fl0m0/ReBox/doc/datasheets/switch/1533612989.png

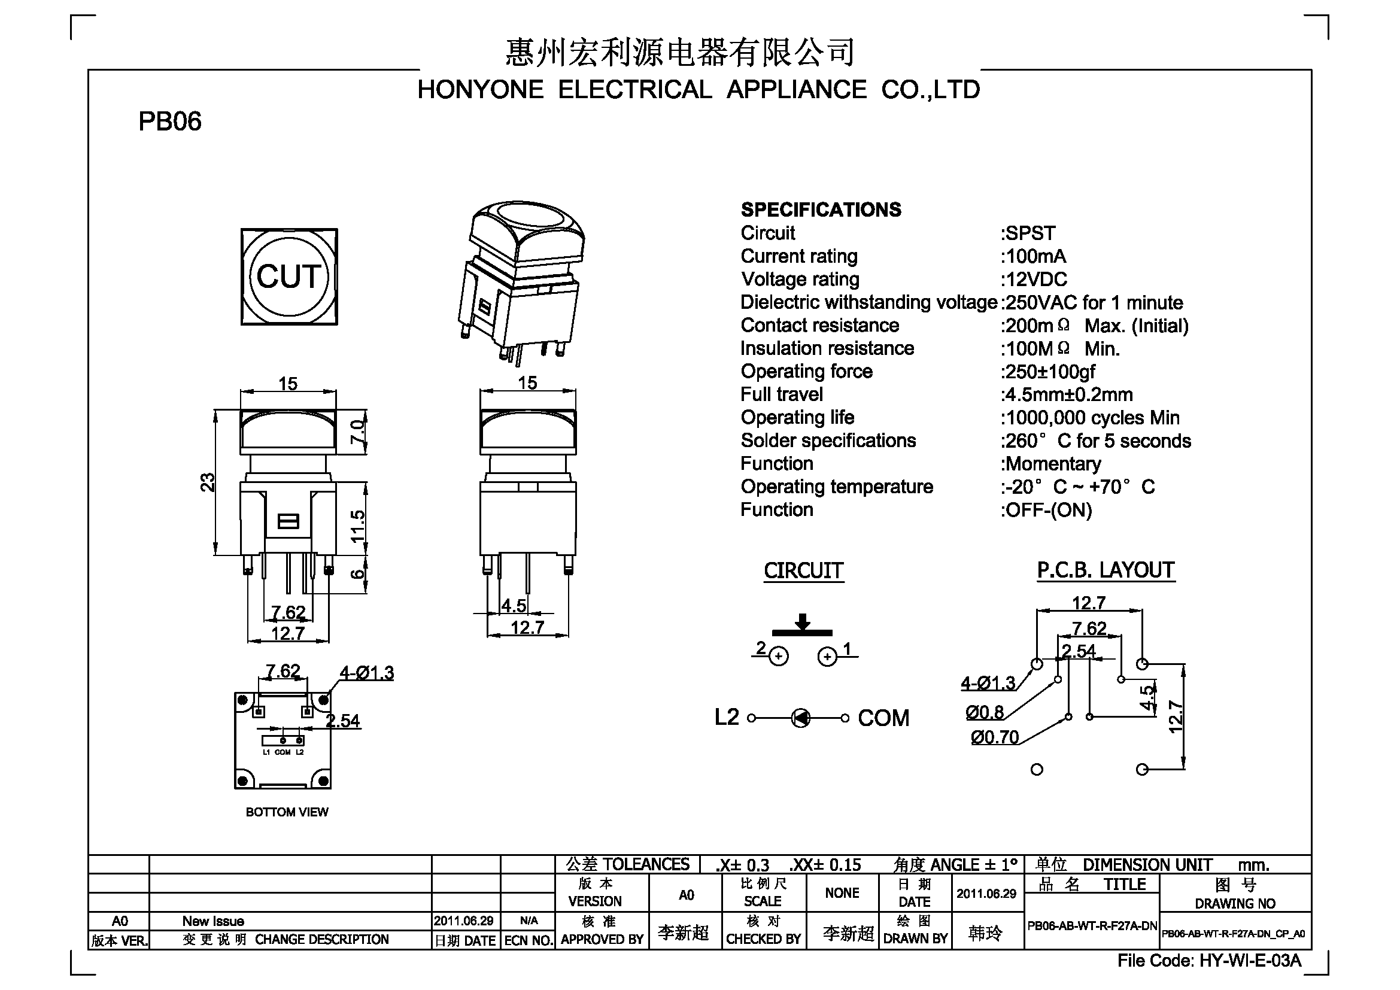
doc/datasheets/switch/1533612989.png
