fl0m0/ReBox/doc/datasheets/switch/20211209145039_88595.jpg

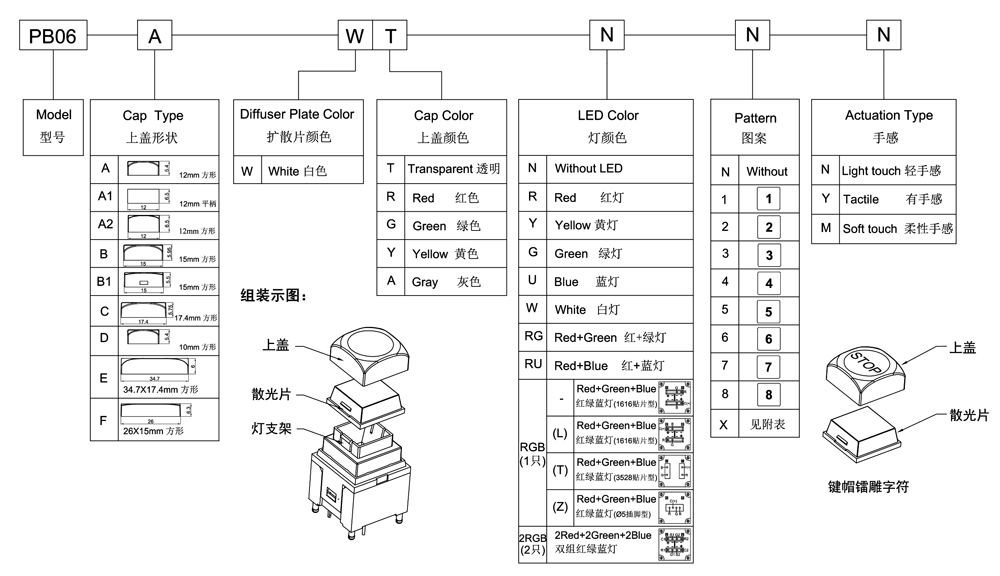
doc/datasheets/switch/20211209145039_88595.jpg
