fl0m0/ReBox/doc/datasheets/switch/20211209151750_96506.jpg

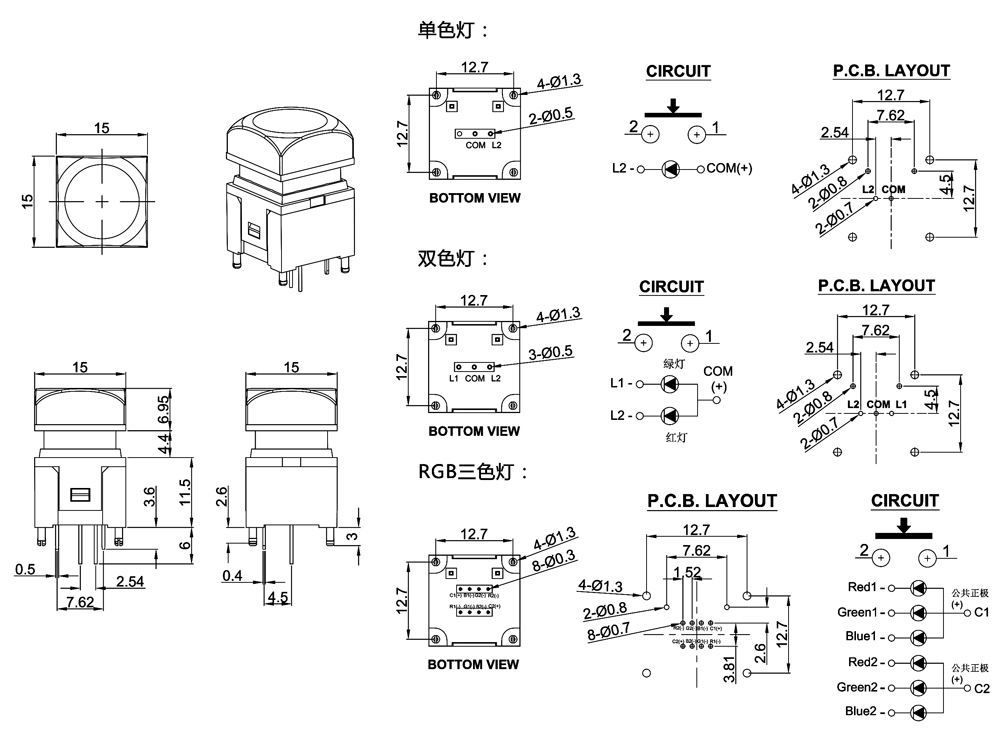
doc/datasheets/switch/20211209151750_96506.jpg
