fl0m0/ReBox/sim/relay_driver.asc

C1: cap; 22µ; Rser=0.2
C2: cap; 470n
D1: schottky; BAT54
D2: zener; BZX84B12VL
L1: ind; 200m
M1: nmos; BSH103BK
M2: nmos; BSH103BK
R1: res; 46
R2: res; 330k
R3: res; 47
V1: voltage; 5; Rser=0.1
V2: voltage; PULSE(0 5 1m 10n 10n 250m 300m)
Named nets: 0, +5, Drain, Gate1, Gate2
.tran 310m
.inc BSH103BK.lib
