fl0m0/ReBox/pcb/ReBox_A1/MCU.kicad_sch

## KiCad design pcb/ReBox_A1/MCU.kicad_sch (2025-03-04)

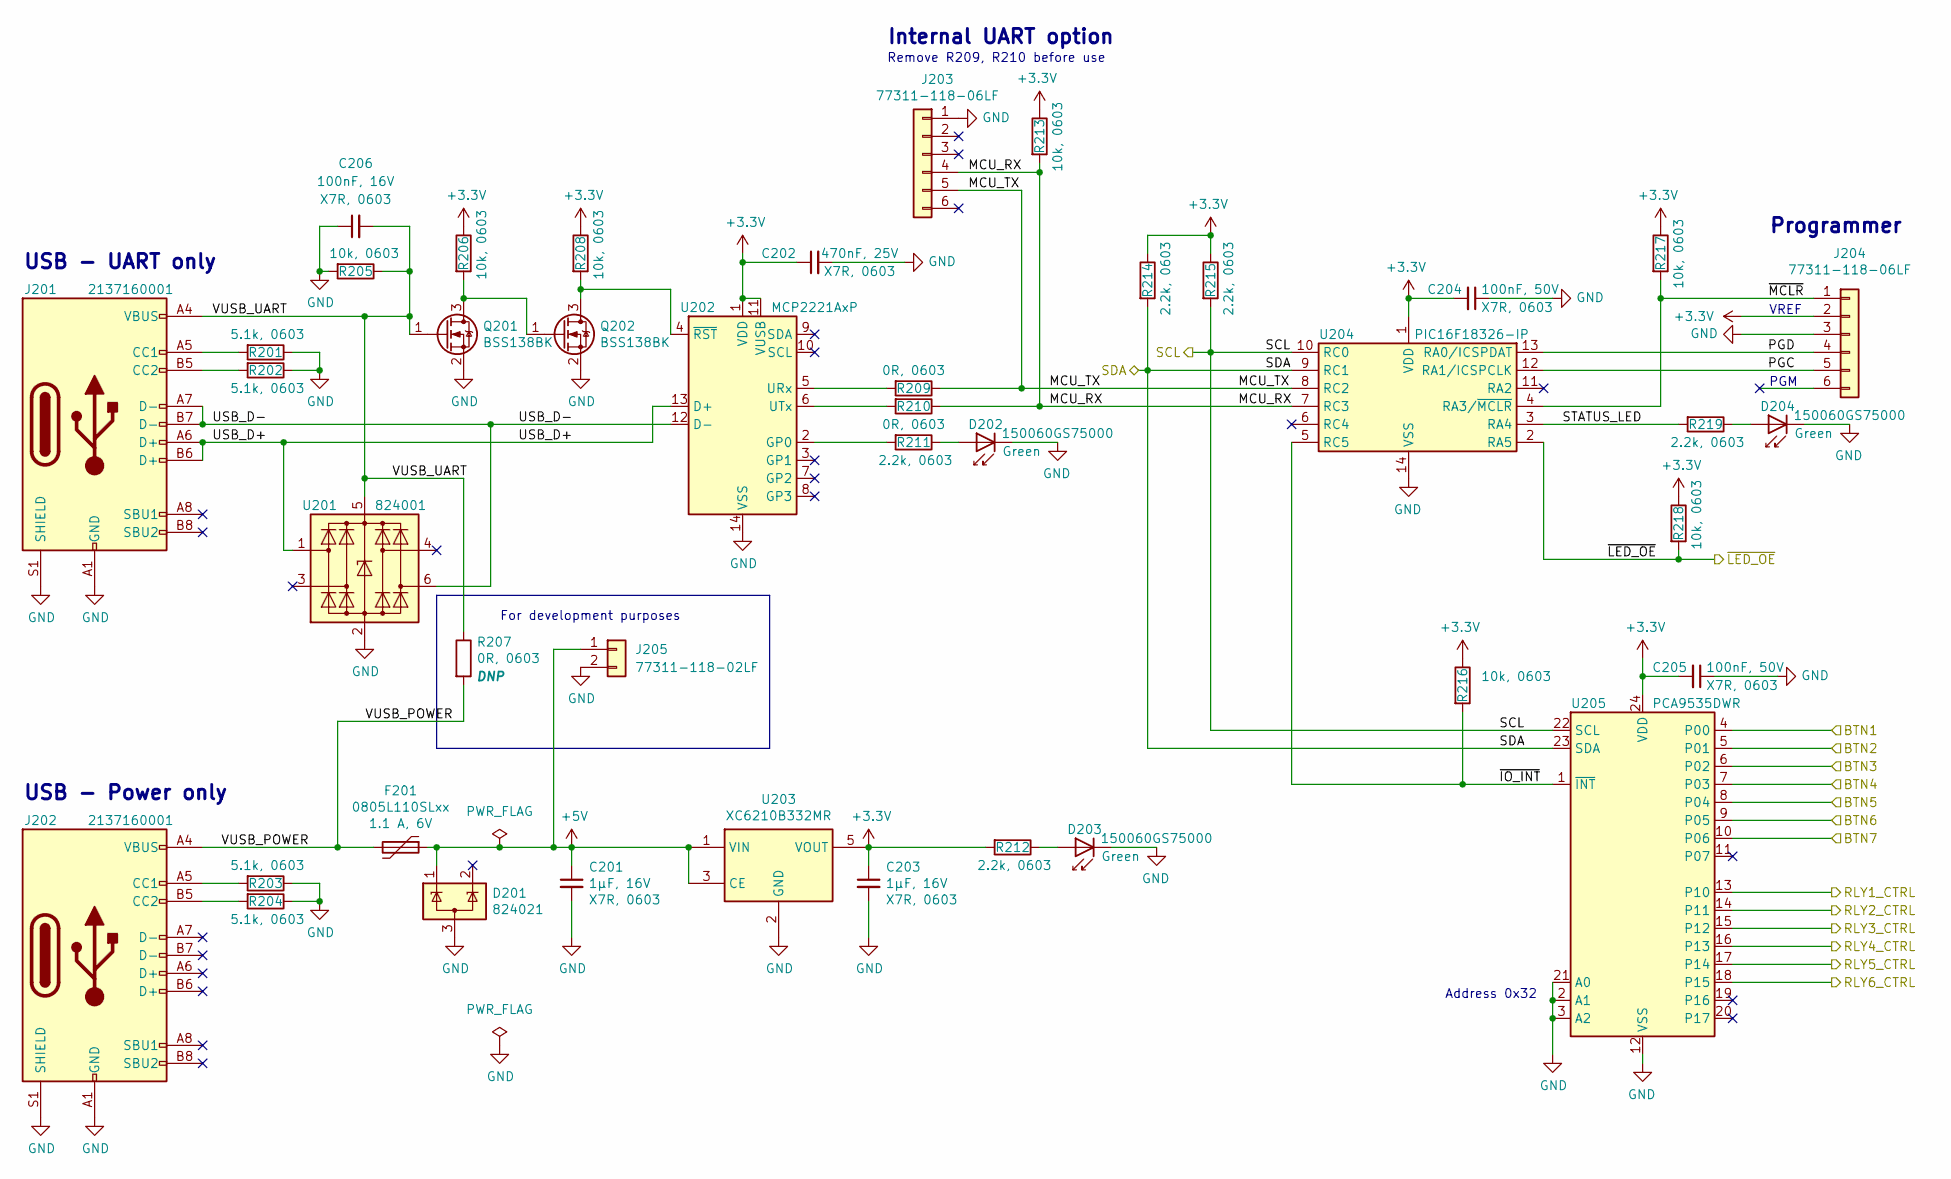
[picture p20: schematic MCU.kicad_sch]

Parts:
C201, C203: 1uF,16V,X7R,0603; C_0603_1608Metric_Pad1.08x0.95mm_HandSolder
C202: 470nF,25V,X7R,0603; C_0603_1608Metric_Pad1.08x0.95mm_HandSolder
C204, C205: 100nF,50V,X7R,0603; C_0603_1608Metric_Pad1.08x0.95mm_HandSolder
C206: 100nF,16V,X7R,0603; C_0603_1608Metric_Pad1.08x0.95mm_HandSolder
D201: 824021; SOT-23_Handsoldering
D202, D203, D204: 150060GS75000; LED_0603_1608Metric_Pad1.05x0.95mm_HandSolder
F201: 0805L110SLxx; Fuse_0805_2012Metric_Pad1.15x1.40mm_HandSolder
J201, J202: 2137160001; USB_C_Receptacle_Molex_2137160001
J203, J204: 77311-118-06LF; PinHeader_1x06_P2.54mm_Vertical
J205: 77311-118-02LF; PinHeader_1x02_P2.54mm_Vertical
Q201, Q202: BSS138BK; SOT-23_Handsoldering
R201, R202, R203, R204: 5.1k,0603; R_0603_1608Metric_Pad0.98x0.95mm_HandSolder
R205, R206, R208, R213, R216, R217, R218: 10k,0603; R_0603_1608Metric_Pad0.98x0.95mm_HandSolder
R207, R209, R210: 0R,0603; R_0603_1608Metric_Pad0.98x0.95mm_HandSolder
R211, R212, R214, R215, R219: 2.2k,0603; R_0603_1608Metric_Pad0.98x0.95mm_HandSolder
U201: 824001; SOT-23-6_Handsoldering
U202: MCP2221AxP; DIP-14_W7.62mm
U203: XC6210B332MR; SOT-23-5
U204: PIC16F18326-IP; DIP-14_W7.62mm
U205: PCA9535DWR; SOIC-24W_7.5x15.4mm_P1.27mm

Connections:
+3.3V: C202.1, C203.1, C204.2, C205.2, J204.2, R206.1, R208.1, R212.2, R213.1, R214.1, R215.1, R216.1, R217.1, R218.1, U202.1 (VDD), U202.11 (VUSB), U203.5 (VOUT), U204.1 (VDD), U205.24 (VDD)
+5V: C201.1, D201.1 (K), F201.1, J205.1, U203.1 (VIN), U203.3 (CE)
BTN1: U205.4 (P00)
BTN2: U205.5 (P01)
BTN3: U205.6 (P02)
BTN4: U205.7 (P03)
BTN5: U205.8 (P04)
BTN6: U205.9 (P05)
BTN7: U205.10 (P06)
GND: C201.2, C202.2, C203.2, C204.1, C205.1, C206.1, D201.3 (A), D202.1 (K), D203.1 (K), D204.1 (K), J201.A1 (GND), J201.A12 (GND), J201.B1 (GND), J201.B12 (GND), J201.S1 (SHIELD), J202.A1 (GND), J202.A12 (GND), J202.B1 (GND), J202.B12 (GND), J202.S1 (SHIELD), J203.1, J204.3, J205.2, Q201.2 (S), Q202.2 (S), R201.1, R202.1, R203.1, R204.1, R205.2, U201.2 (GND), U202.14 (VSS), U203.2 (GND), U204.14 (VSS), U205.2 (A1), U205.3 (A2), U205.12 (VSS), U205.21 (A0)
MCU_RX: J203.4, R210.1, R213.2, U204.7 (RC3)
MCU_TX: J203.5, R209.1, U204.8 (RC2)
unnamed: D202.2 (A), R211.1
unnamed: D203.2 (A), R212.1
unnamed: D204.2 (A), R219.1
unnamed: J201.A5 (CC1), R201.2
unnamed: J201.B5 (CC2), R202.2
unnamed: J202.A5 (CC1), R203.2
unnamed: J202.B5 (CC2), R204.2
unnamed: Q201.3 (D), Q202.1 (G), R206.2
unnamed: Q202.3 (D), R208.2, U202.4 (~RST)
unnamed: R209.2, U202.5 (URx)
unnamed: R210.2, U202.6 (UTx)
unnamed: R211.2, U202.2 (GP0)
PGC: J204.5, U204.12 (RA1/ICSPCLK)
PGD: J204.4, U204.13 (RA0/ICSPDAT)
RLY1_CTRL: U205.13 (P10)
RLY2_CTRL: U205.14 (P11)
RLY3_CTRL: U205.15 (P12)
RLY4_CTRL: U205.16 (P13)
RLY5_CTRL: U205.17 (P14)
RLY6_CTRL: U205.18 (P15)
SCL: R215.2, U204.10 (RC0), U205.22 (SCL)
SDA: R214.2, U204.9 (RC1), U205.23 (SDA)
STATUS_LED: R219.2, U204.3 (RA4)
USB_D+: J201.A6 (D+), J201.B6 (D+), U201.1 (I/O1), U202.13 (D+)
USB_D-: J201.A7 (D-), J201.B7 (D-), U201.6 (I/O4), U202.12 (D-)
VUSB_POWER: F201.2, J202.A4 (VBUS), J202.A9 (VBUS), J202.B4 (VBUS), J202.B9 (VBUS), R207.2
VUSB_UART: C206.2, J201.A4 (VBUS), J201.A9 (VBUS), J201.B4 (VBUS), J201.B9 (VBUS), Q201.1 (G), R205.1, R207.1, U201.5 (VBUS)
~IO_INT: R216.2, U204.5 (RC5), U205.1 (~INT)
~LED_OE: R218.2, U204.2 (RA5)
~MCLR: J204.1, R217.2, U204.4 (RA3/~MCLR)

Notes on the sheet:
Programmer
PGM
Address 0x32
Internal UART option
For development purposes
USB - UART only
Remove R209, R210 before use
VREF
USB - Power only
