fl0m0/ReBox/pcb/ReBox_A1/Relais.kicad_sch

## KiCad design pcb/ReBox_A1/Relais.kicad_sch (2025-03-04)

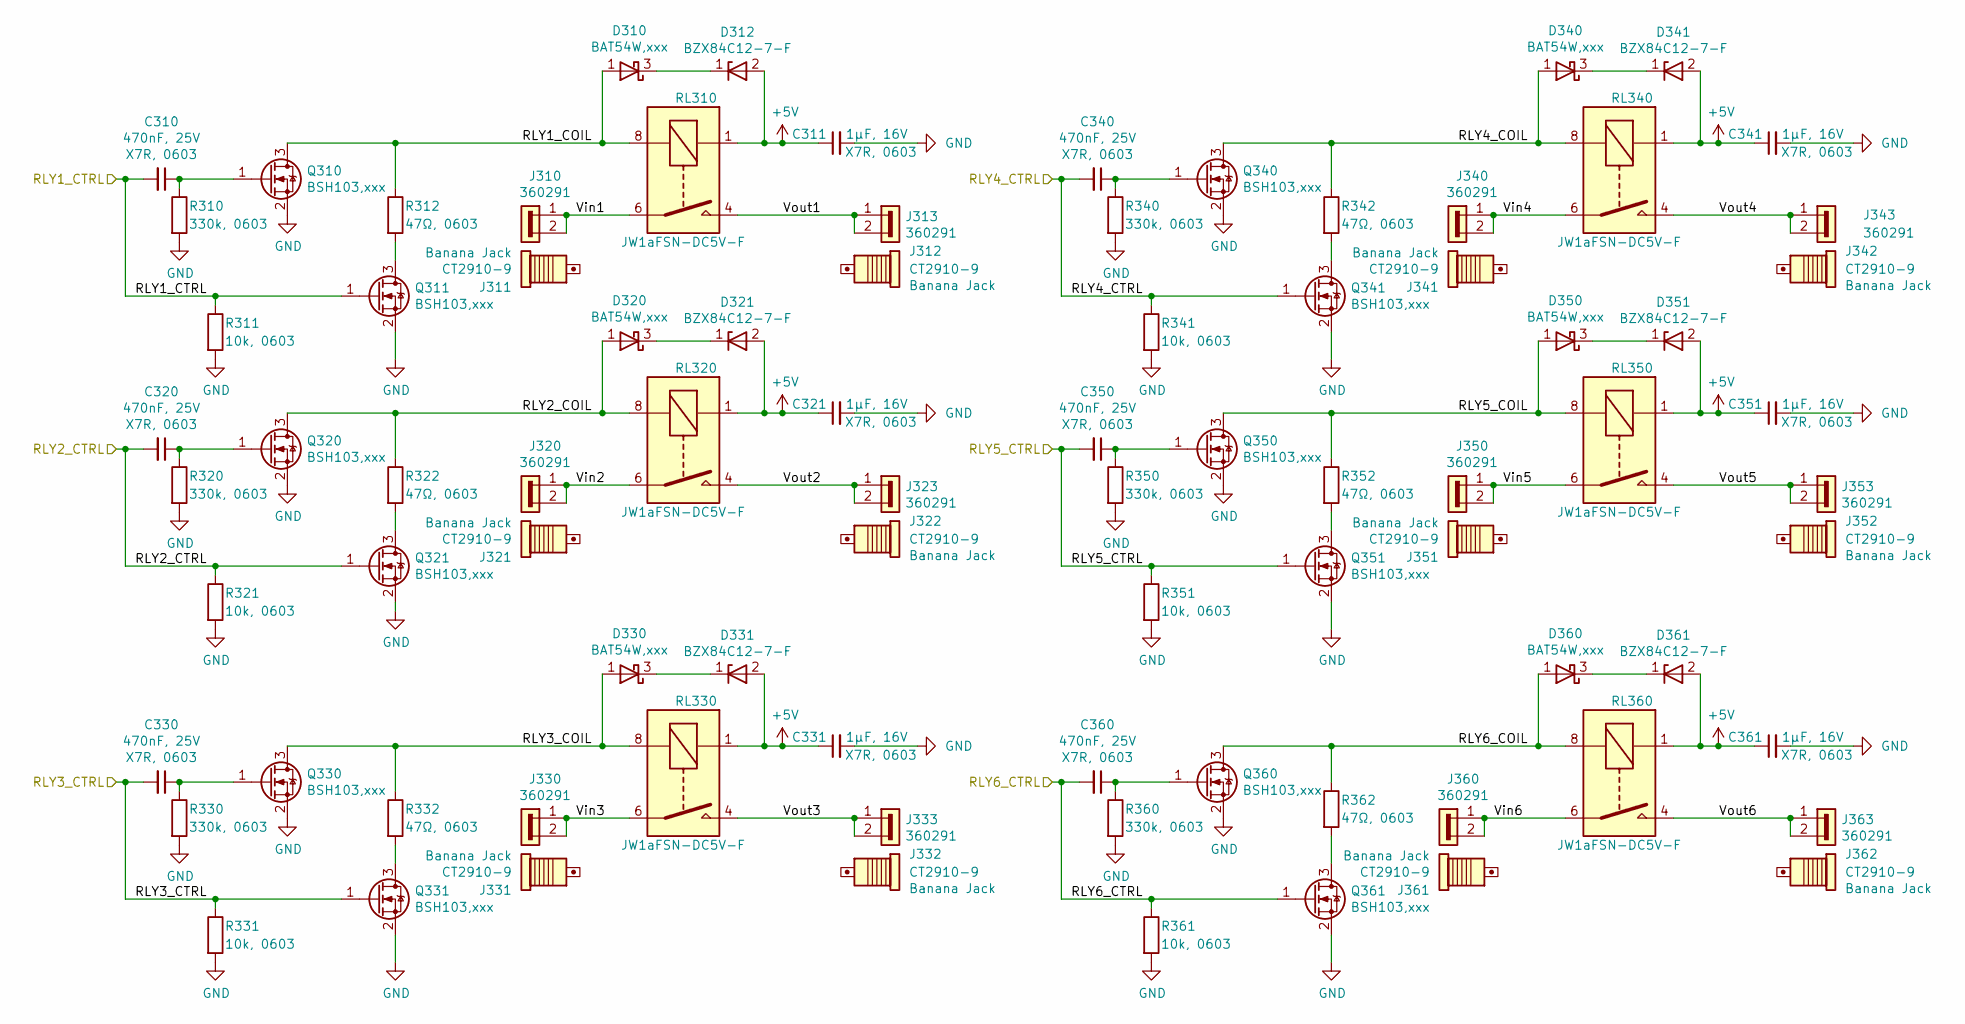
[picture p21: schematic Relais.kicad_sch]

Parts:
C310, C320, C330, C340, C350, C360: 470nF,25V,X7R,0603; C_0603_1608Metric_Pad1.08x0.95mm_HandSolder
C311, C321, C331, C341, C351, C361: 1uF,16V,X7R,0603; C_0603_1608Metric_Pad1.08x0.95mm_HandSolder
D310, D320, D330, D340, D350, D360: BAT54W,xxx; SOT-323_SC-70_Handsoldering
D312, D321, D331, D341, D351, D361: BZX84C12-7-F; D_SOT-23_ANK_Handsoldering
J310, J313, J320, J323, J330, J333, J340, J343, J350, J353, J360, J363: 360291; Terminal_Block_Metz_Connect_360291
J311, J312, J321, J322, J331, J332, J341, J342, J351, J352, J361, J362: CT2910-9; Banana_Jack_Cal_Test_Electronics_CT2910-9_No_Silkscreen
Q310, Q311, Q320, Q321, Q330, Q331, Q340, Q341, Q350, Q351, Q360, Q361: BSH103,xxx; SOT-23_Handsoldering
R310, R320, R330, R340, R350, R360: 330k,0603; R_0603_1608Metric_Pad0.98x0.95mm_HandSolder
R311, R321, R331, R341, R351, R361: 10k,0603; R_0603_1608Metric_Pad0.98x0.95mm_HandSolder
R312, R322, R332, R342, R352, R362: 47R,1206; R_1206_3216Metric_Pad1.30x1.75mm_HandSolder
RL310, RL320, RL330, RL340, RL350, RL360: JW1aFSN-DC5V-F; Relay_SPST_Panasonic_JW1_FormA

Connections:
+5V: C311.1, C321.1, C331.1, C341.1, C351.1, C361.1, D312.2 (A), D321.2 (A), D331.2 (A), D341.2 (A), D351.2 (A), D361.2 (A), RL310.1, RL320.1, RL330.1, RL340.1, RL350.1, RL360.1
GND: C311.2, C321.2, C331.2, C341.2, C351.2, C361.2, Q310.2 (S), Q311.2 (S), Q320.2 (S), Q321.2 (S), Q330.2 (S), Q331.2 (S), Q340.2 (S), Q341.2 (S), Q350.2 (S), Q351.2 (S), Q360.2 (S), Q361.2 (S), R310.2, R311.2, R320.2, R321.2, R330.2, R331.2, R340.2, R341.2, R350.2, R351.2, R360.2, R361.2
unnamed: C310.1, Q310.1 (G), R310.1
unnamed: C320.1, Q320.1 (G), R320.1
unnamed: C330.1, Q330.1 (G), R330.1
unnamed: C340.1, Q340.1 (G), R340.1
unnamed: C350.1, Q350.1 (G), R350.1
unnamed: C360.1, Q360.1 (G), R360.1
unnamed: D310.3 (K), D312.1 (K)
unnamed: D320.3 (K), D321.1 (K)
unnamed: D330.3 (K), D331.1 (K)
unnamed: D340.3 (K), D341.1 (K)
unnamed: D350.3 (K), D351.1 (K)
unnamed: D360.3 (K), D361.1 (K)
unnamed: Q311.3 (D), R312.2
unnamed: Q321.3 (D), R322.2
unnamed: Q331.3 (D), R332.2
unnamed: Q341.3 (D), R342.2
unnamed: Q351.3 (D), R352.2
unnamed: Q361.3 (D), R362.2
RLY1_COIL: D310.1 (A), Q310.3 (D), R312.1, RL310.8
RLY1_CTRL: C310.2, Q311.1 (G), R311.1
RLY2_COIL: D320.1 (A), Q320.3 (D), R322.1, RL320.8
RLY2_CTRL: C320.2, Q321.1 (G), R321.1
RLY3_COIL: D330.1 (A), Q330.3 (D), R332.1, RL330.8
RLY3_CTRL: C330.2, Q331.1 (G), R331.1
RLY4_COIL: D340.1 (A), Q340.3 (D), R342.1, RL340.8
RLY4_CTRL: C340.2, Q341.1 (G), R341.1
RLY5_COIL: D350.1 (A), Q350.3 (D), R352.1, RL350.8
RLY5_CTRL: C350.2, Q351.1 (G), R351.1
RLY6_COIL: D360.1 (A), Q360.3 (D), R362.1, RL360.8
RLY6_CTRL: C360.2, Q361.1 (G), R361.1
Vin1: J310.1, J310.2, RL310.6
Vin2: J320.1, J320.2, RL320.6
Vin3: J330.1, J330.2, RL330.6
Vin4: J340.1, J340.2, RL340.6
Vin5: J350.1, J350.2, RL350.6
Vin6: J360.1, J360.2, RL360.6
Vout1: J313.1, J313.2, RL310.4
Vout2: J323.1, J323.2, RL320.4
Vout3: J333.1, J333.2, RL330.4
Vout4: J343.1, J343.2, RL340.4
Vout5: J353.1, J353.2, RL350.4
Vout6: J363.1, J363.2, RL360.4
