fl0m0/ReBox/pcb/ReBox_A1/Switches.kicad_sch

## KiCad design pcb/ReBox_A1/Switches.kicad_sch (2025-03-04)

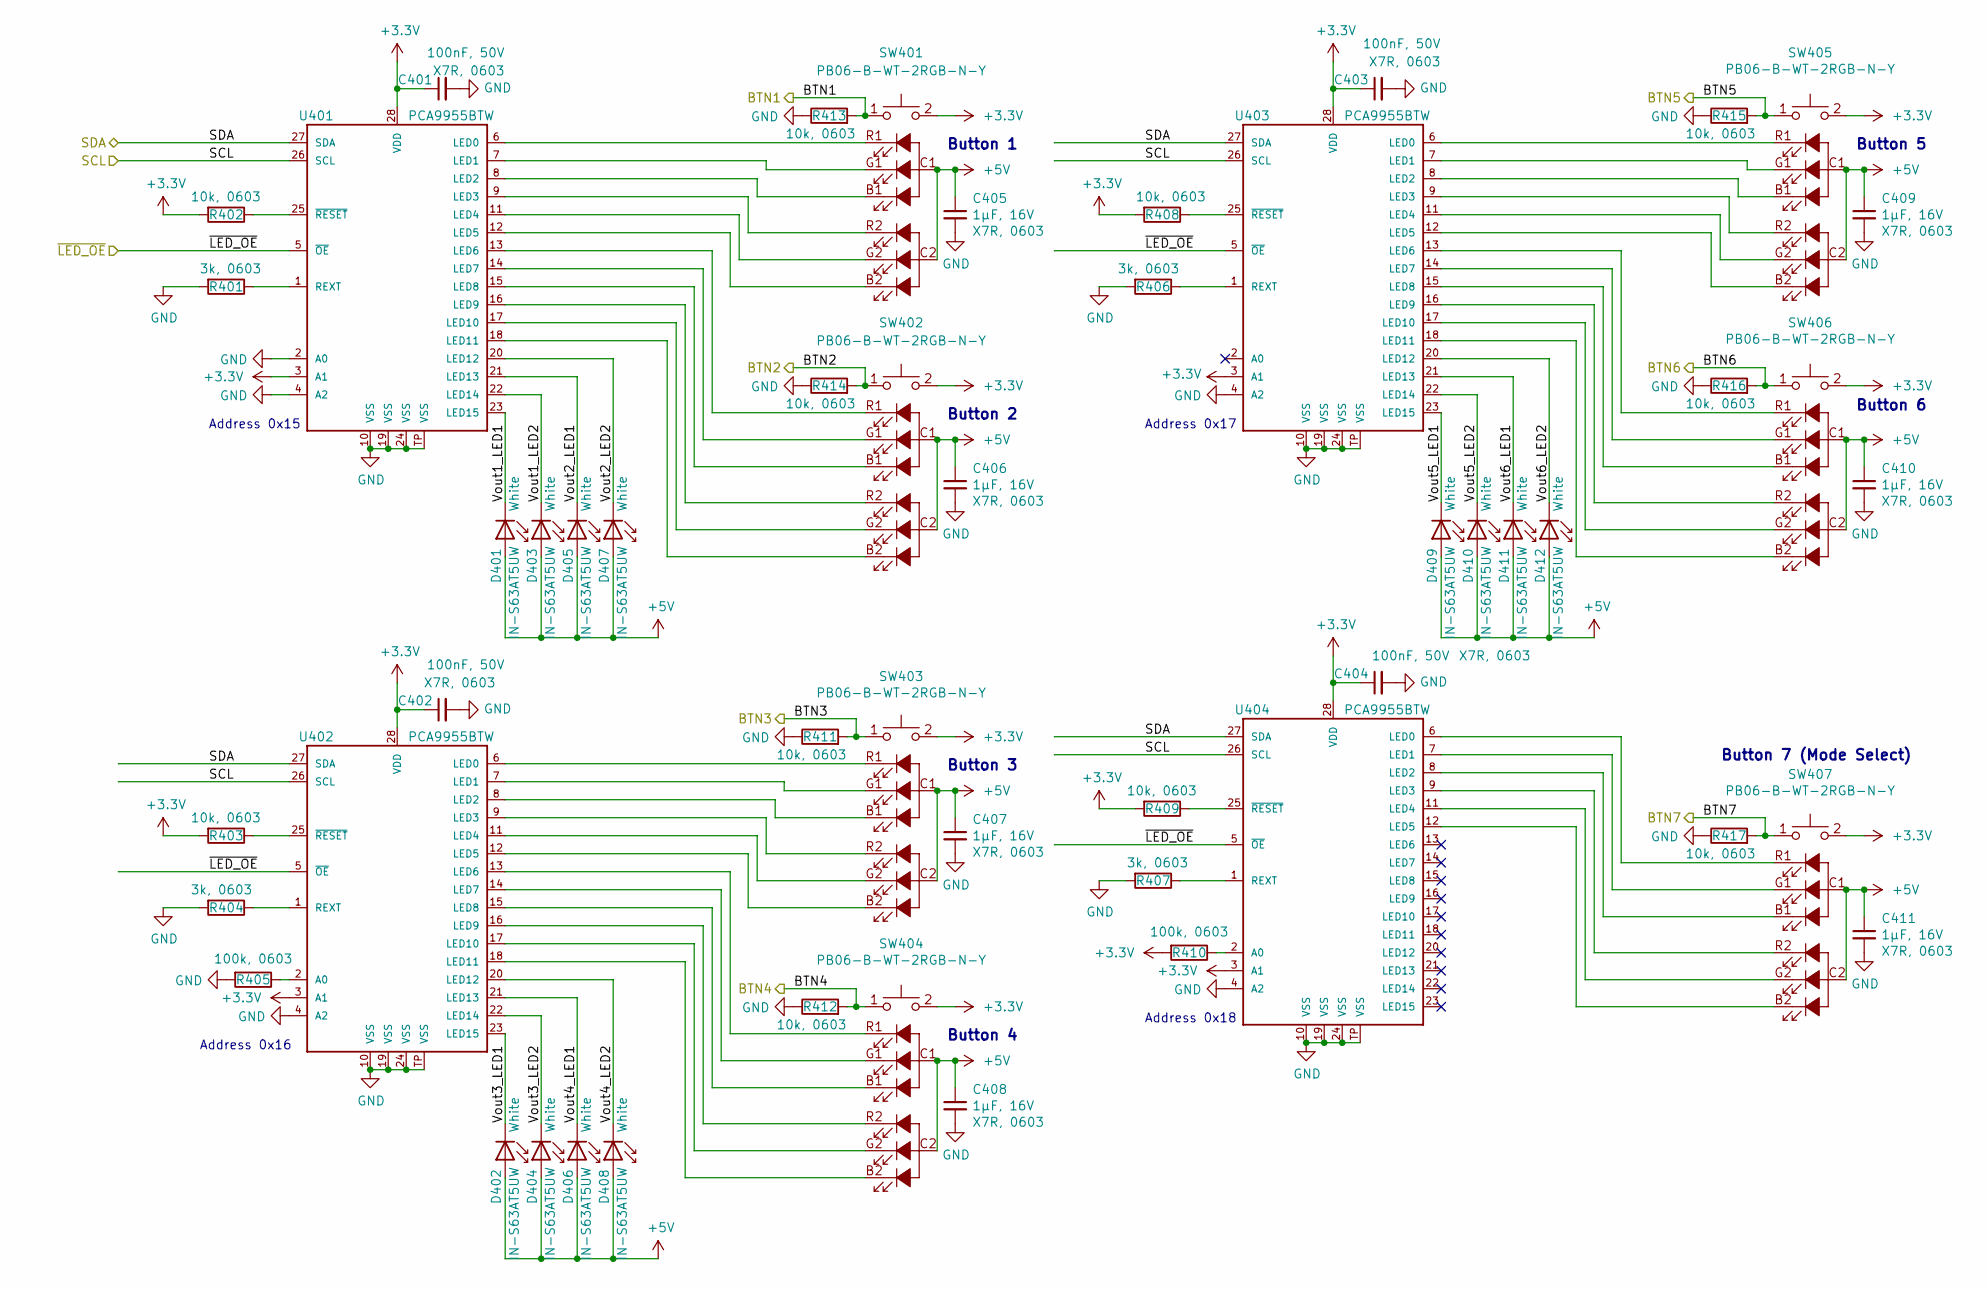
[picture p22: schematic Switches.kicad_sch]

Parts:
C401, C402, C403, C404: 100nF,50V,X7R,0603; C_0603_1608Metric_Pad1.08x0.95mm_HandSolder
C405, C406, C407, C408, C409, C410, C411: 1uF,16V,X7R,0603; C_0603_1608Metric_Pad1.08x0.95mm_HandSolder
D401, D402, D403, D404, D405, D406, D407, D408, D409, D410, D411, D412: IN-S63AT5UW; LED_0603_1608Metric_Low_Profile
R401, R404, R406, R407: 3k,0603; R_0603_1608Metric_Pad0.98x0.95mm_HandSolder
R402, R403, R408, R409, R411, R412, R413, R414, R415, R416, R417: 10k,0603; R_0603_1608Metric_Pad0.98x0.95mm_HandSolder
R405, R410: 100k,0603; R_0603_1608Metric_Pad0.98x0.95mm_HandSolder
SW401, SW402, SW403, SW404, SW405, SW406, SW407: PB06-B-WT-2RGB-N-Y; PB06-B-Wx-2RGB-x-x
U401, U402, U403, U404: PCA9955BTW; HTSSOP28_EP

Connections:
+3.3V: C401.1, C402.1, C403.1, C404.1, R402.2, R403.2, R408.2, R409.2, R410.2, SW401.2, SW402.2, SW403.2, SW404.2, SW405.2, SW406.2, SW407.2, U401.3 (A1), U401.28 (VDD), U402.3 (A1), U402.28 (VDD), U403.3 (A1), U403.28 (VDD), U404.3 (A1), U404.28 (VDD)
+5V: C405.1, C406.1, C407.1, C408.1, C409.1, C410.1, C411.1, D401.2 (A), D402.2 (A), D403.2 (A), D404.2 (A), D405.2 (A), D406.2 (A), D407.2 (A), D408.2 (A), D409.2 (A), D410.2 (A), D411.2 (A), D412.2 (A), SW401.C1 (A), SW401.C2 (A), SW402.C1 (A), SW402.C2 (A), SW403.C1 (A), SW403.C2 (A), SW404.C1 (A), SW404.C2 (A), SW405.C1 (A), SW405.C2 (A), SW406.C1 (A), SW406.C2 (A), SW407.C1 (A), SW407.C2 (A)
BTN1: R413.2, SW401.1
BTN2: R414.2, SW402.1
BTN3: R411.2, SW403.1
BTN4: R412.2, SW404.1
BTN5: R415.2, SW405.1
BTN6: R416.2, SW406.1
BTN7: R417.2, SW407.1
GND: C401.2, C402.2, C403.2, C404.2, C405.2, C406.2, C407.2, C408.2, C409.2, C410.2, C411.2, R401.2, R404.2, R405.2, R406.2, R407.2, R411.1, R412.1, R413.1, R414.1, R415.1, R416.1, R417.1, U401.2 (A0), U401.4 (A2), U401.10 (VSS), U401.19 (VSS), U401.24 (VSS), U401.TP (VSS), U402.4 (A2), U402.10 (VSS), U402.19 (VSS), U402.24 (VSS), U402.TP (VSS), U403.4 (A2), U403.10 (VSS), U403.19 (VSS), U403.24 (VSS), U403.TP (VSS), U404.4 (A2), U404.10 (VSS), U404.19 (VSS), U404.24 (VSS), U404.TP (VSS)
unnamed: R401.1, U401.1 (REXT)
unnamed: R402.1, U401.25 (~RESET)
unnamed: R403.1, U402.25 (~RESET)
unnamed: R404.1, U402.1 (REXT)
unnamed: R405.1, U402.2 (A0)
unnamed: R406.1, U403.1 (REXT)
unnamed: R407.1, U404.1 (REXT)
unnamed: R408.1, U403.25 (~RESET)
unnamed: R409.1, U404.25 (~RESET)
unnamed: R410.1, U404.2 (A0)
unnamed: SW401.B1 (K), U401.8 (LED2)
unnamed: SW401.B2 (K), U401.12 (LED5)
unnamed: SW401.G1 (K), U401.7 (LED1)
unnamed: SW401.G2 (K), U401.11 (LED4)
unnamed: SW401.R1 (K), U401.6 (LED0)
unnamed: SW401.R2 (K), U401.9 (LED3)
unnamed: SW402.B1 (K), U401.15 (LED8)
unnamed: SW402.B2 (K), U401.18 (LED11)
unnamed: SW402.G1 (K), U401.14 (LED7)
unnamed: SW402.G2 (K), U401.17 (LED10)
unnamed: SW402.R1 (K), U401.13 (LED6)
unnamed: SW402.R2 (K), U401.16 (LED9)
unnamed: SW403.B1 (K), U402.8 (LED2)
unnamed: SW403.B2 (K), U402.12 (LED5)
unnamed: SW403.G1 (K), U402.7 (LED1)
unnamed: SW403.G2 (K), U402.11 (LED4)
unnamed: SW403.R1 (K), U402.6 (LED0)
unnamed: SW403.R2 (K), U402.9 (LED3)
unnamed: SW404.B1 (K), U402.15 (LED8)
unnamed: SW404.B2 (K), U402.18 (LED11)
unnamed: SW404.G1 (K), U402.14 (LED7)
unnamed: SW404.G2 (K), U402.17 (LED10)
unnamed: SW404.R1 (K), U402.13 (LED6)
unnamed: SW404.R2 (K), U402.16 (LED9)
unnamed: SW405.B1 (K), U403.8 (LED2)
unnamed: SW405.B2 (K), U403.12 (LED5)
unnamed: SW405.G1 (K), U403.7 (LED1)
unnamed: SW405.G2 (K), U403.11 (LED4)
unnamed: SW405.R1 (K), U403.6 (LED0)
unnamed: SW405.R2 (K), U403.9 (LED3)
unnamed: SW406.B1 (K), U403.15 (LED8)
unnamed: SW406.B2 (K), U403.18 (LED11)
unnamed: SW406.G1 (K), U403.14 (LED7)
unnamed: SW406.G2 (K), U403.17 (LED10)
unnamed: SW406.R1 (K), U403.13 (LED6)
unnamed: SW406.R2 (K), U403.16 (LED9)
unnamed: SW407.B1 (K), U404.8 (LED2)
unnamed: SW407.B2 (K), U404.12 (LED5)
unnamed: SW407.G1 (K), U404.7 (LED1)
unnamed: SW407.G2 (K), U404.11 (LED4)
unnamed: SW407.R1 (K), U404.6 (LED0)
unnamed: SW407.R2 (K), U404.9 (LED3)
SCL: U401.26 (SCL), U402.26 (SCL), U403.26 (SCL), U404.26 (SCL)
SDA: U401.27 (SDA), U402.27 (SDA), U403.27 (SDA), U404.27 (SDA)
Vout1_LED1: D401.1 (K), U401.23 (LED15)
Vout1_LED2: D403.1 (K), U401.22 (LED14)
Vout2_LED1: D405.1 (K), U401.21 (LED13)
Vout2_LED2: D407.1 (K), U401.20 (LED12)
Vout3_LED1: D402.1 (K), U402.23 (LED15)
Vout3_LED2: D404.1 (K), U402.22 (LED14)
Vout4_LED1: D406.1 (K), U402.21 (LED13)
Vout4_LED2: D408.1 (K), U402.20 (LED12)
Vout5_LED1: D409.1 (K), U403.23 (LED15)
Vout5_LED2: D410.1 (K), U403.22 (LED14)
Vout6_LED1: D411.1 (K), U403.21 (LED13)
Vout6_LED2: D412.1 (K), U403.20 (LED12)
~LED_OE: U401.5 (~OE), U402.5 (~OE), U403.5 (~OE), U404.5 (~OE)

Notes on the sheet:
Button 2
Button 5
Button 4
Button 7 (Mode Select)
Address 0x17
Button 1
Address 0x18
Button 6
Address 0x16
Address 0x15
Button 3
